puddletowntom/BTC-Price-Ticker/schematic/schematic.png

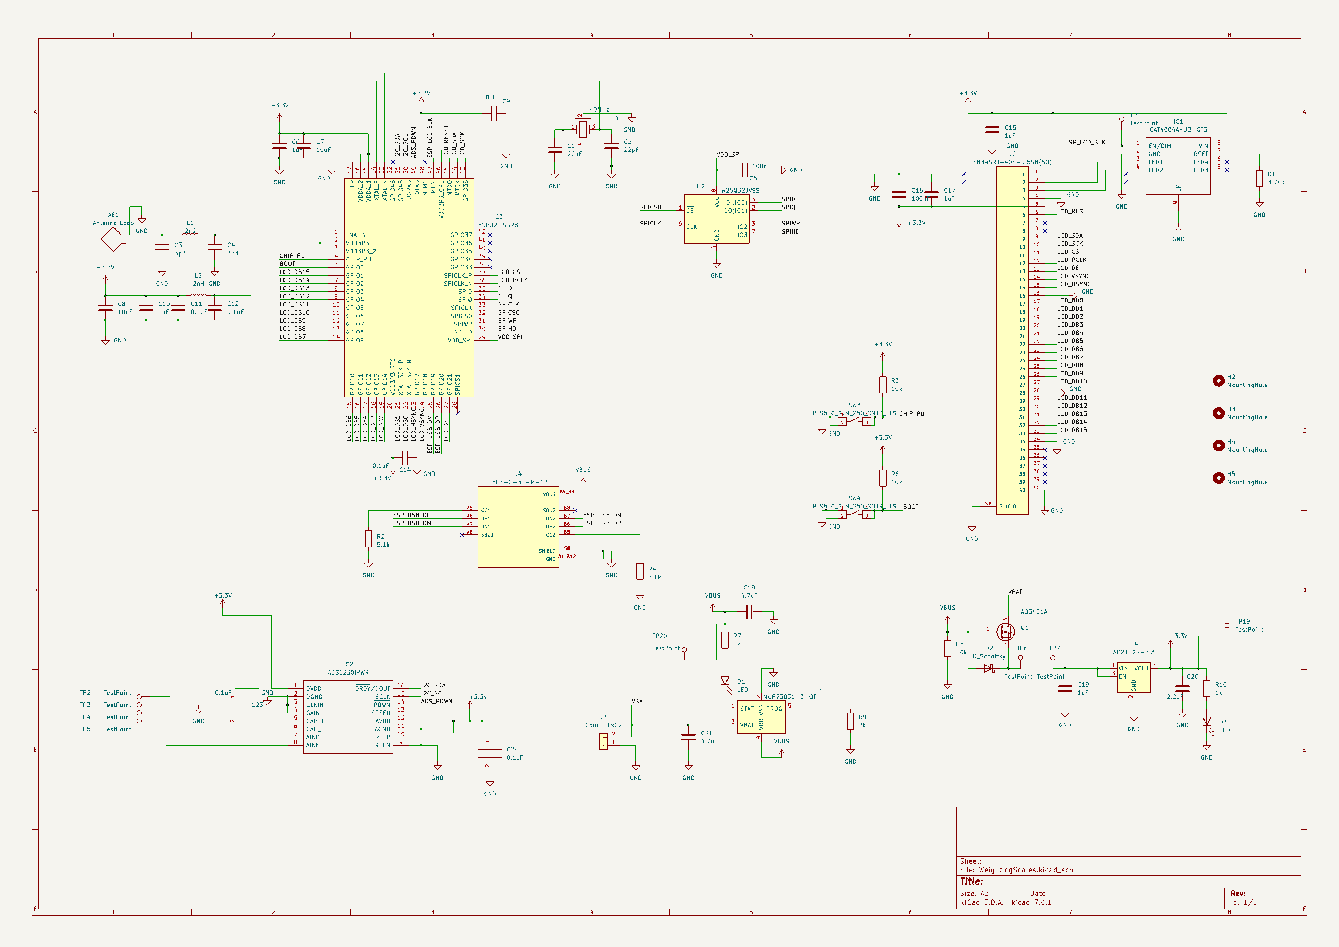
schematic/schematic.png
